FranHawk/esp32-smart-pow/2.software/esp32_justgui/src/images.h

#ifndef IMAGES_H
#define IMAGES_H

#include <lvgl.h>

#ifndef LV_ATTRIBUTE_MEM_ALIGN
#define LV_ATTRIBUTE_MEM_ALIGN
#endif

#ifndef LV_ATTRIBUTE_IMG_ABC
#define LV_ATTRIBUTE_IMG_ABC
#endif

const LV_ATTRIBUTE_MEM_ALIGN LV_ATTRIBUTE_LARGE_CONST LV_ATTRIBUTE_IMG_ABC uint8_t abc_map[] = {
  0x05, 0x04, 0x09, 0xff, 	/*Color of index 0*/
  0x6f, 0x8b, 0x97, 0xff, 	/*Color of index 1*/
  0x6d, 0xca, 0xf2, 0xff, 	/*Color of index 2*/
  0x30, 0x48, 0x5a, 0xff, 	/*Color of index 3*/
  0xfa, 0xfd, 0xfc, 0xff, 	/*Color of index 4*/
  0x59, 0x9f, 0xcc, 0xff, 	/*Color of index 5*/
  0x25, 0x5b, 0x84, 0xff, 	/*Color of index 6*/
  0x23, 0x37, 0x4e, 0xff, 	/*Color of index 7*/
  0xc0, 0xd0, 0xe1, 0xff, 	/*Color of index 8*/
  0x86, 0xab, 0xb6, 0xff, 	/*Color of index 9*/
  0x84, 0xb7, 0xcd, 0xff, 	/*Color of index 10*/
  0x4e, 0x73, 0x8e, 0xff, 	/*Color of index 11*/
  0x1f, 0x2b, 0x39, 0xff, 	/*Color of index 12*/
  0x4c, 0x64, 0x71, 0xff, 	/*Color of index 13*/
  0x74, 0x94, 0xac, 0xff, 	/*Color of index 14*/
  0x6d, 0xbc, 0xeb, 0xff, 	/*Color of index 15*/

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
  0x44, 0x44, 0x44, 0x44, 0x44, 0x44, 0x44, 0x44, 0x44, 0x44, 0x44, 0x44, 0x44, 0x44, 0x44, 0x44, 0x44, 0x44, 0x44, 0x44, 0x44, 0x44, 0x44, 0x44, 0x44, 0x44, 0x44, 0x44, 0x44, 0x44, 0x44, 0x44, 0x44, 0x44, 0x44, 0x44, 0x44, 0x44, 0x44, 0x44, 0x44, 0x44, 0x44, 0x44, 0x44, 0x44, 0x44, 0x44, 0x44, 0x44, 0x44, 0x44, 0x44, 0x44, 0x44, 0x44, 0x44, 0x44, 0x44, 0x44, 0x44, 0x44, 0x44, 0x44, 0x44, 0x44, 0x44, 0x44, 0x44, 0x44, 0x44, 0x44, 0x44, 0x44, 0x44, 0x44, 0x49, 0x3c, 0x73, 0x7c, 0x00, 0x77, 0x73, 0xc3, 0x84, 0x44, 0x44, 0x44, 0x44, 0x44, 0x44, 0x44, 0x44, 0x44, 0x44, 0x44, 0x44, 0x44, 0x44, 0x44, 
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
};

const lv_img_dsc_t abc = {
  .header.always_zero = 0,
  .header.w = 200,
  .header.h = 200,
  .data_size = 20064,
  .header.cf = LV_IMG_CF_INDEXED_4BIT,
  .data = abc_map,
};

#endif
