FranHawk/esp32-smart-pow/2.software/esp32_justgui/include/display.h

#ifndef DISPLAY_H
#define DISPLAY_H

#include <lvgl.h>

#define LCD_BL_PIN 22
#define LCD_BL_PWM_CHANNEL 0


class Display
{
private:


public:
	void init();
	void routine();
	void setBackLight(float);
};

#endif
