FranHawk/esp32-smart-pow/2.software/esp32_justgui/include/lv_brightness_page.h

#ifndef __LV_BRIGHTNESS_PAGE_H
#define __LV_BRIGHTNESS_PAGE_H

#ifdef __cplusplus
extern "C" {
#endif

#ifdef LV_LVGL_H_INCLUDE_SIMPLE
#include "lvgl.h"
#else
#include "lvgl/lvgl.h"
#endif

void lv_app_load_light_scr(void);

#ifdef __cplusplus
} /* extern "C" */
#endif

#endif
