FranHawk/esp32-smart-pow/2.software/esp32_justgui/include/lv_port_indev.h

/**
 * @file lv_port_indev_templ.h
 *
 */

 /*Copy this file as "lv_port_indev.h" and set this value to "1" to enable content*/


#ifndef LV_PORT_INDEV_TEMPL_H
#define LV_PORT_INDEV_TEMPL_H



	/*********************
	 *      INCLUDES
	 *********************/
#include "lvgl.h"

extern lv_indev_t* indev_encoder;

void lv_port_indev_init(void);




#endif /*LV_PORT_INDEV_TEMPL_H*/
